Kanedinha/Temperature-Control/Assets/Images/Screenshot 2024-01-02 211112.jpg

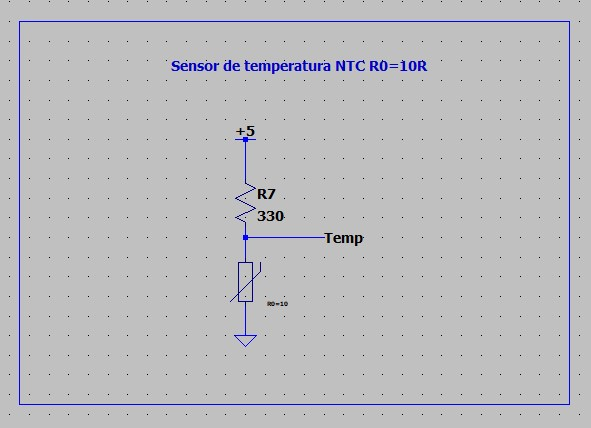
Assets/Images/Screenshot 2024-01-02 211112.jpg
