Kanedinha/Temperature-Control/Assets/Images/Structure_Length.jpg

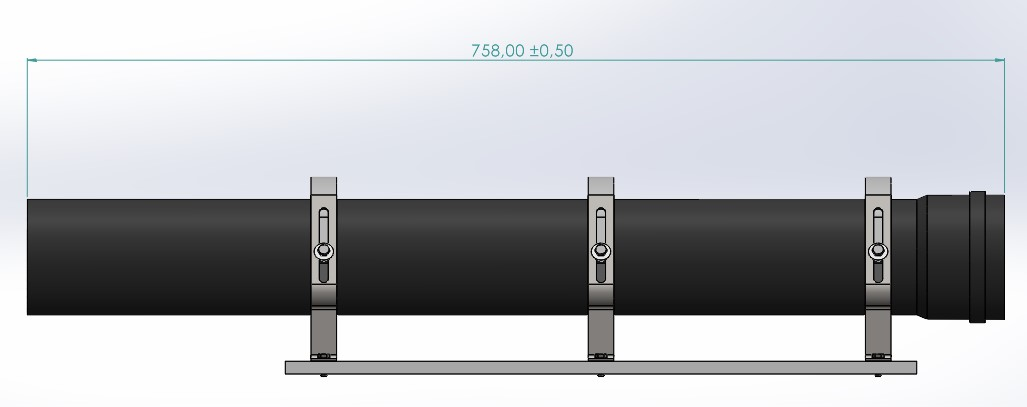
Assets/Images/Structure_Length.jpg
