Kanedinha/Temperature-Control/SystemModeling/bestFit.jpg

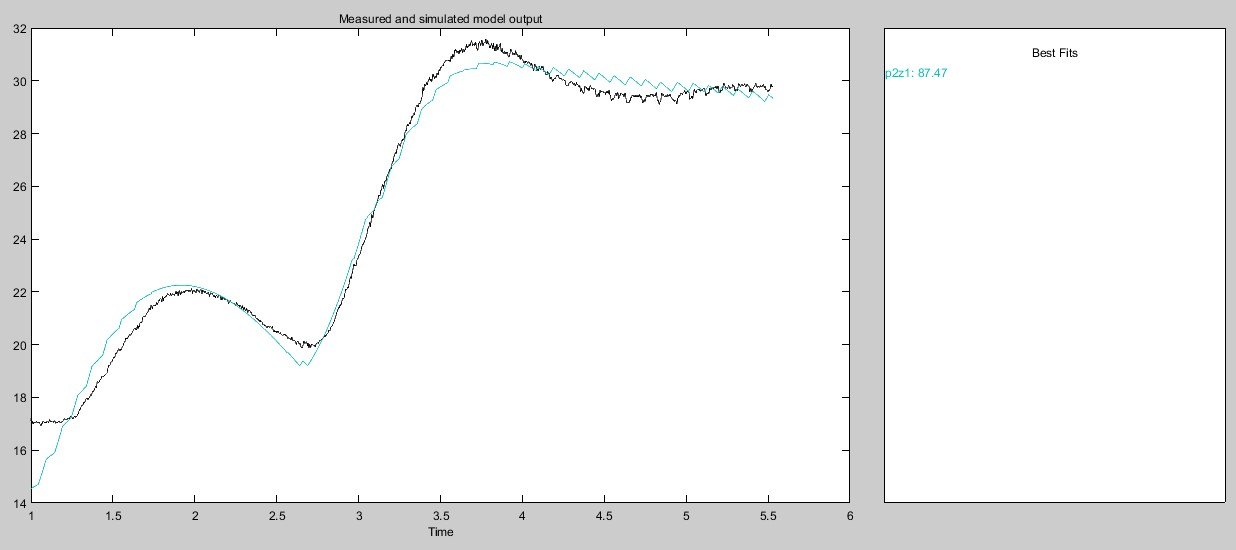
SystemModeling/bestFit.jpg
