Kanedinha/Temperature-Control/SystemModeling/fits_original.jpg

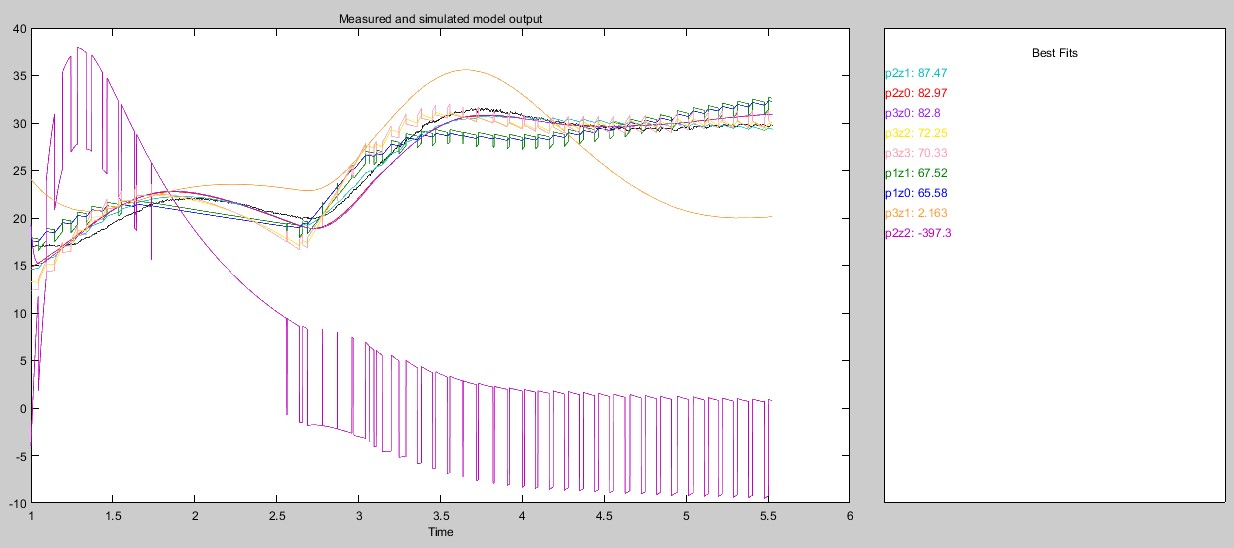
SystemModeling/fits_original.jpg
