Kanedinha/Temperature-Control/SystemModeling/InOut.jpg

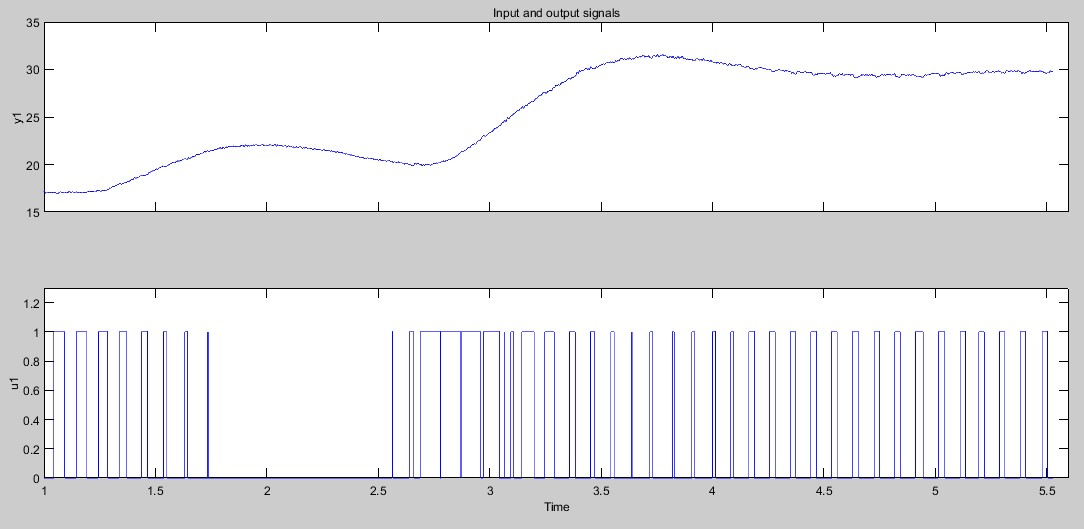
SystemModeling/InOut.jpg
