Kanedinha/Temperature-Control/SystemModeling/RootLocusClosedLoop.jpg

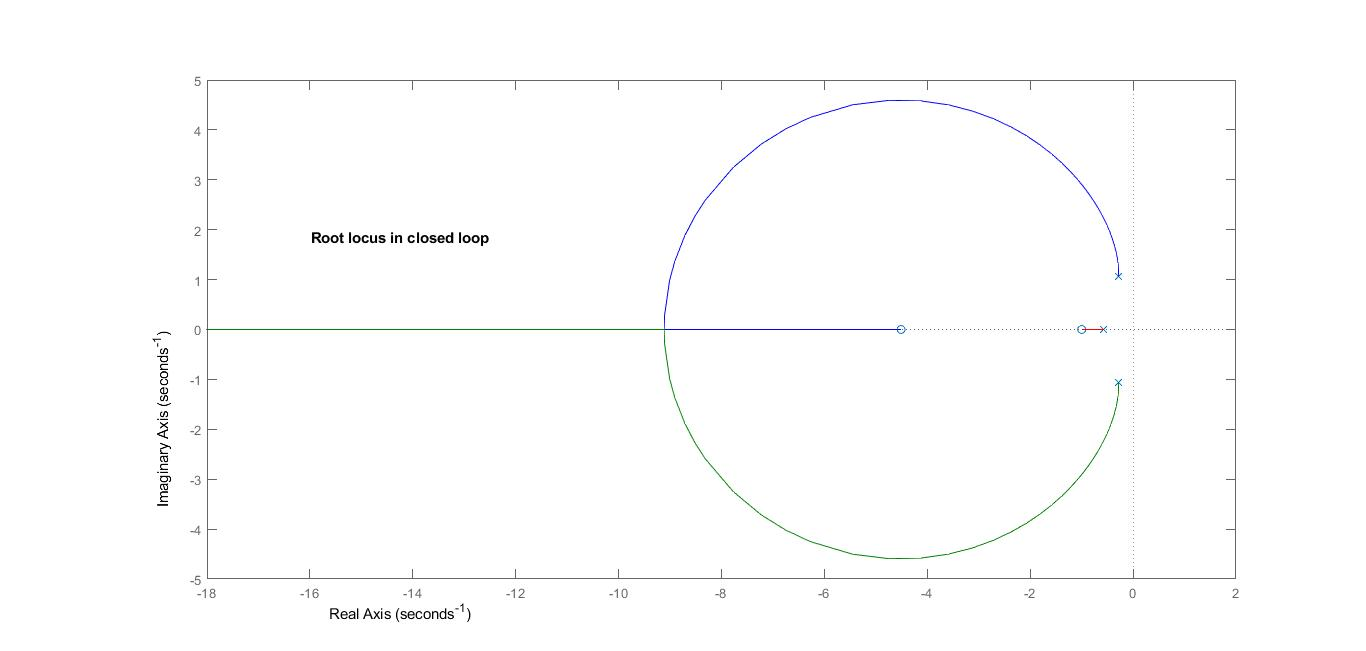
SystemModeling/RootLocusClosedLoop.jpg
