Kanedinha/Temperature-Control/SystemModeling/RootLocusOpenMesh.jpg

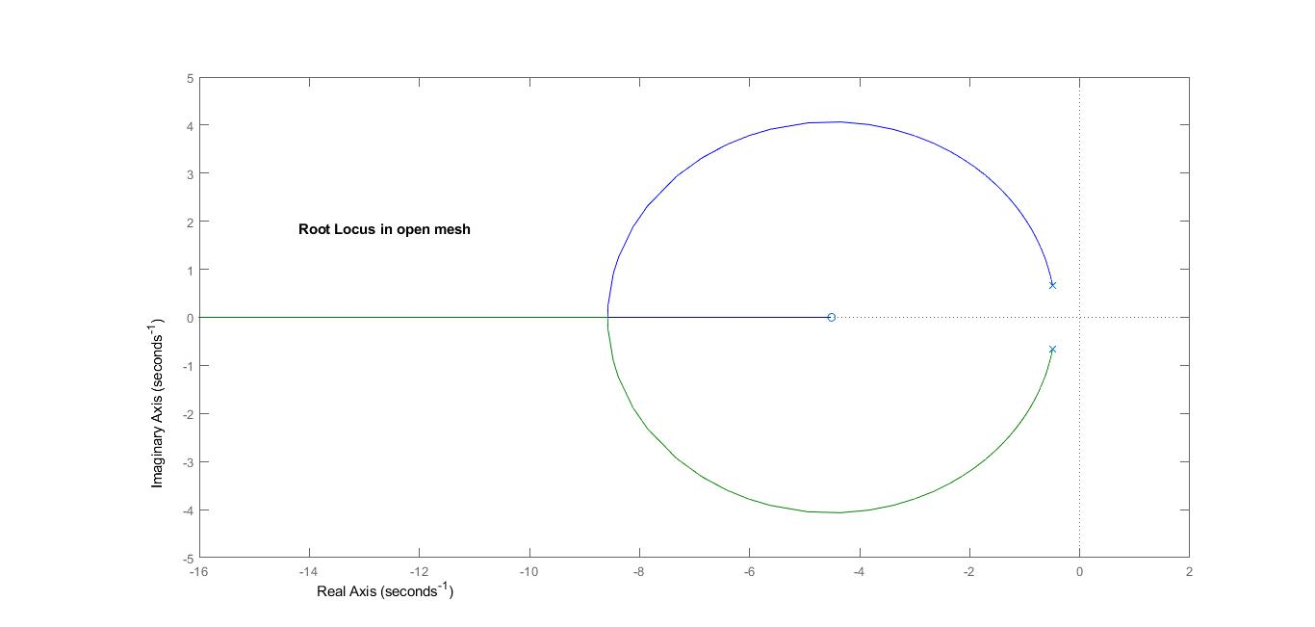
SystemModeling/RootLocusOpenMesh.jpg
