Kanedinha/Temperature-Control/Eletro/Number Of Complete Cycles/HW/Schematic/ZC.asc

ArduinoOut: voltage; PULSE(0 5 0 1u 1u 40m 60m)
C1: cap; 330n
C2: cap; 220n
Digital_Source: voltage; 5
LOAD: res; 35
R1: res; 47
R2: res; 200
R6: res; 510
R7: res; 330
R13: res; 330
Rede: voltage; SINE(0 325 50 0)
U2: MOC3020
U4: BT_TRIAC
U5: ntc_resistor; R0=10
Named nets: 0, +5, Temp, Control, Rede-, Rede+
.tran 0 120m 0 0.1m
Triac U1: BT137
Optotriac: MOC3020
Sensor de temperatura NTC R0=10R
Atuador
Sources
